AlexandruCapatina94/DIY-miniPC-with-AtomicPi/SolidWorks files/PSU Lifters.SLDPRT

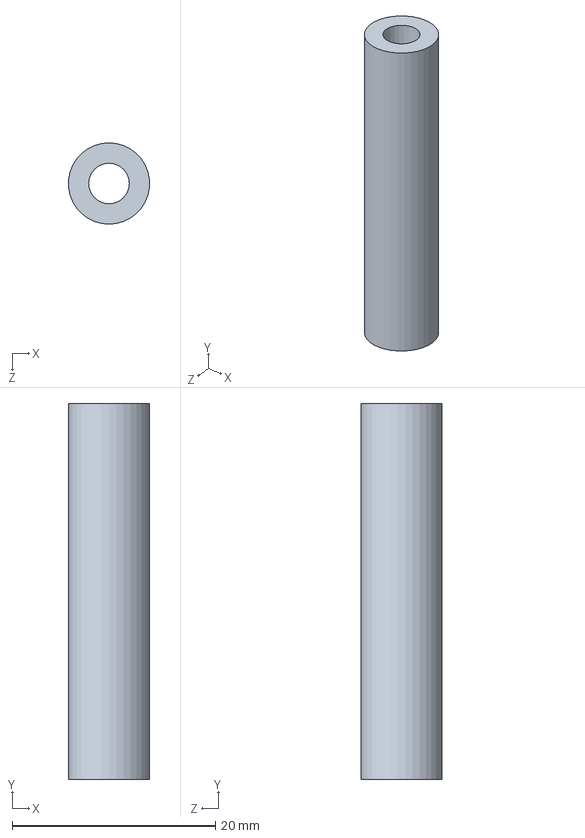
[picture p16: CAD file, 2019-10-19]
SolidWorks files/PSU Lifters.SLDPRT
7.97 x 37.0 x 8.00 mm
