AlexandruCapatina94/DIY-miniPC-with-AtomicPi/SolidWorks files/Top plate.SLDPRT

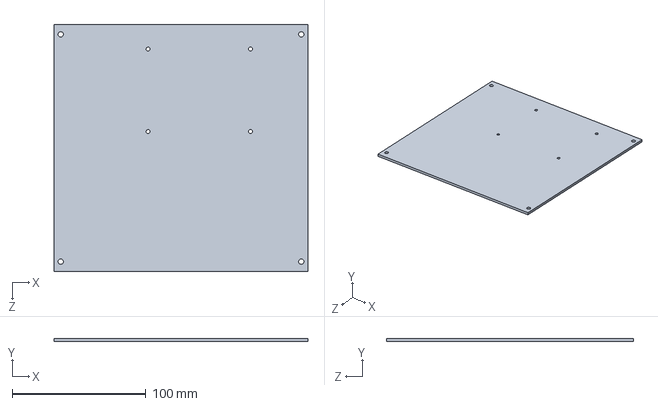
[picture p17: CAD file, 2019-10-19]
SolidWorks files/Top plate.SLDPRT
190.0 x 2.50 x 185.0 mm
