AlexandruCapatina94/DIY-miniPC-with-AtomicPi/SolidWorks files/API Lifters.SLDPRT

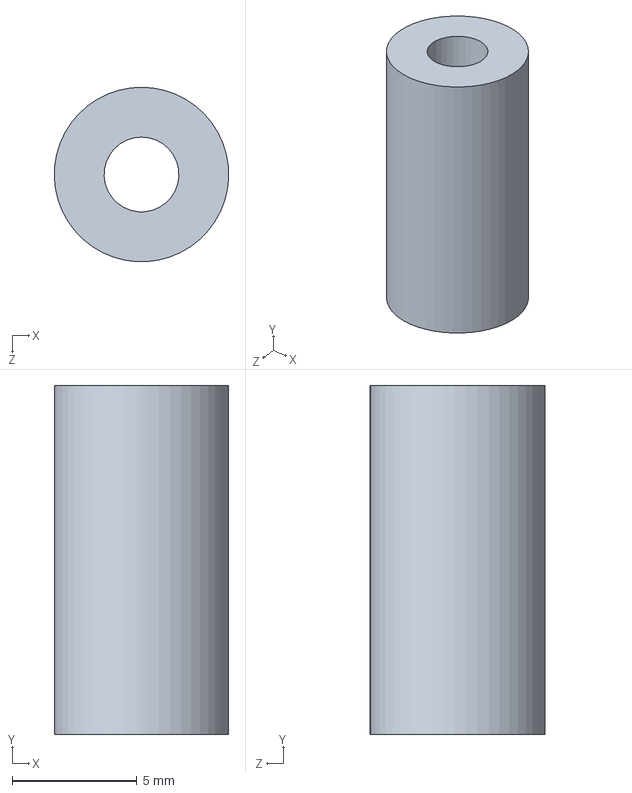
[picture p18: CAD file, 2019-10-19]
SolidWorks files/API Lifters.SLDPRT
7.00 x 14.0 x 7.00 mm
