AlexandruCapatina94/DIY-miniPC-with-AtomicPi/SolidWorks files/AC Power Socket.SLDPRT

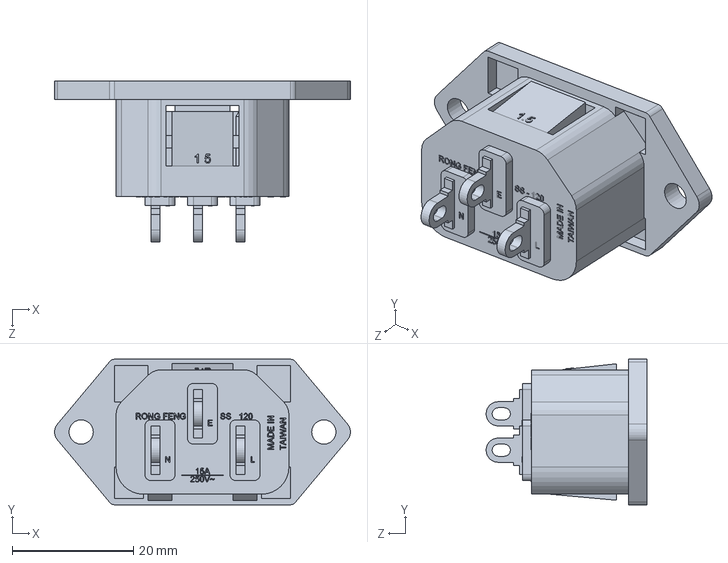
[picture p19: CAD file, 2019-10-19]
SolidWorks files/AC Power Socket.SLDPRT
48.8 x 24.0 x 26.5 mm
