AlexandruCapatina94/DIY-miniPC-with-AtomicPi/SolidWorks files/Back plate.SLDPRT

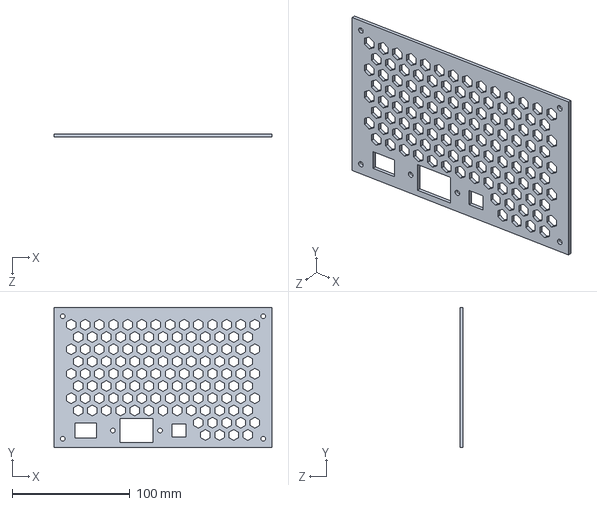
[picture p20: CAD file, 2019-10-19]
SolidWorks files/Back plate.SLDPRT
185.0 x 119.0 x 2.50 mm
