AlexandruCapatina94/DIY-miniPC-with-AtomicPi/SolidWorks files/FAN Shield.SLDPRT

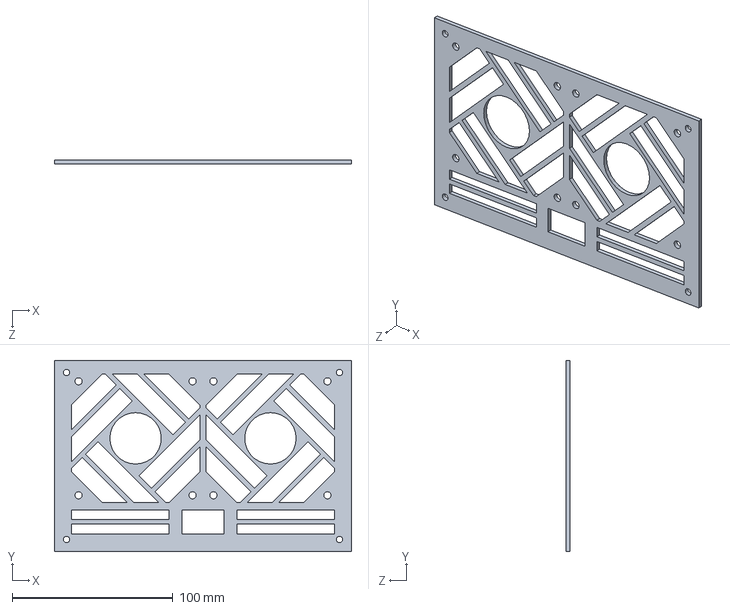
[picture p21: CAD file, 2019-10-19]
SolidWorks files/FAN Shield.SLDPRT
185.0 x 119.0 x 2.50 mm
